Jos-Luijten/online-radiation-lab-robot/design and models of mechanics/Polymer sheet pmma models/tube binder left v1.step

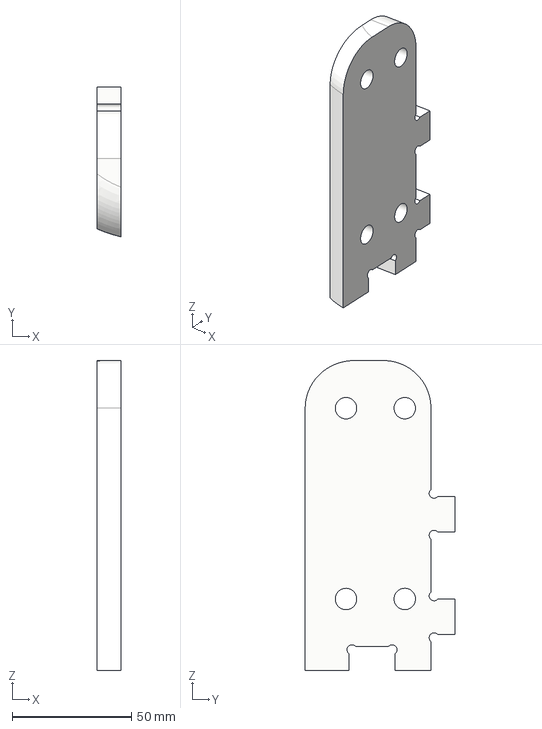
[picture p20: CAD file, 2024-03-11]
design and models of mechanics/Polymer sheet pmma models/tube binder left v1.step
10.0 x 62.8 x 130.0 mm
