Jos-Luijten/online-radiation-lab-robot/design and models of mechanics/objects from other vendors/corner bracket for 20x20 rail v1.step

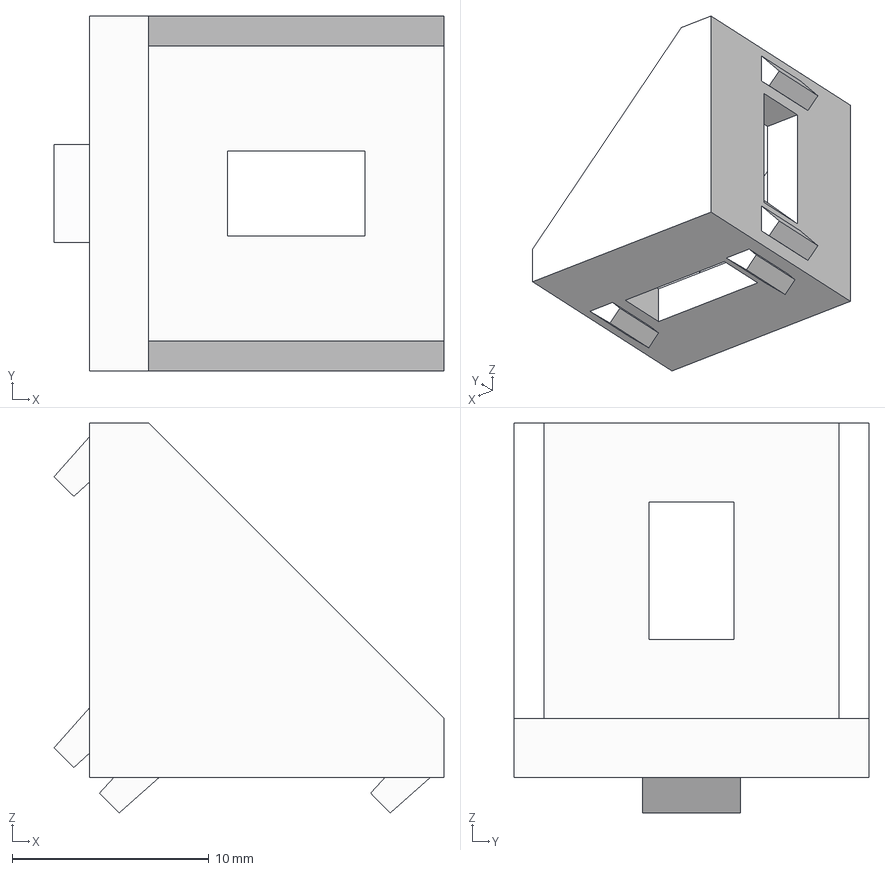
[picture p21: CAD file, 2024-03-11]
design and models of mechanics/objects from other vendors/corner bracket for 20x20 rail v1.step
19.8 x 18.0 x 19.8 mm
