Jos-Luijten/online-radiation-lab-robot/design and models of mechanics/Polymer sheet pmma models/base plate v1.step

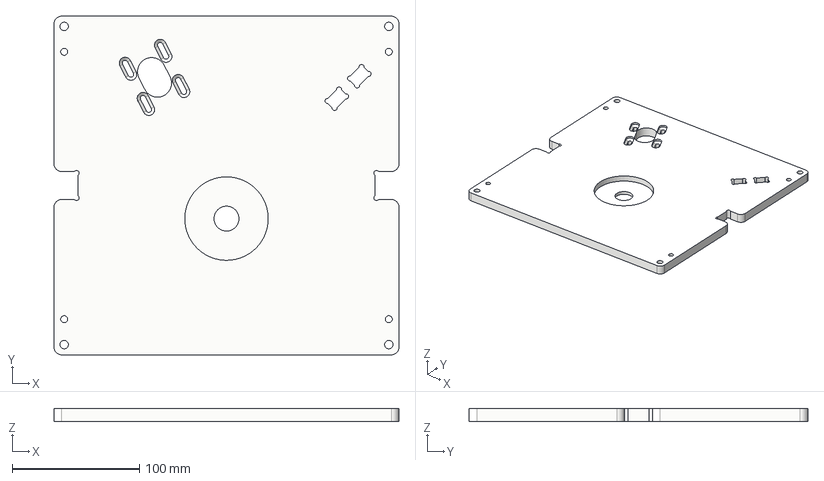
[picture p22: CAD file, 2024-03-11]
design and models of mechanics/Polymer sheet pmma models/base plate v1.step
271.0 x 266.0 x 10.0 mm
