Jos-Luijten/online-radiation-lab-robot/design and models of mechanics/objects from other vendors/T connector for 20x20 rail v1.step

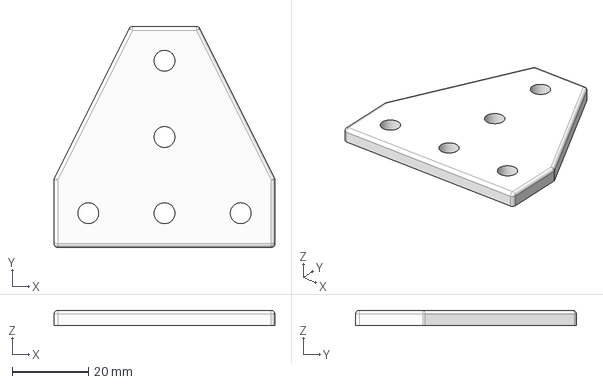
[picture p23: CAD file, 2024-03-11]
design and models of mechanics/objects from other vendors/T connector for 20x20 rail v1.step
58.0 x 58.0 x 4.00 mm
