Jos-Luijten/online-radiation-lab-robot/design and models of mechanics/Polymer sheet pmma models/rotation sensor plate v1.step

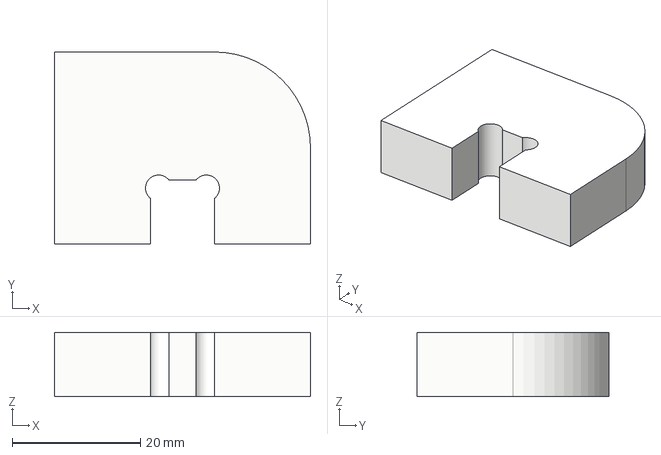
[picture p24: CAD file, 2024-03-11]
design and models of mechanics/Polymer sheet pmma models/rotation sensor plate v1.step
40.0 x 30.0 x 10.0 mm
