Jos-Luijten/online-radiation-lab-robot/design and models of mechanics/objects from other vendors/bracket for nema 17 v1.step

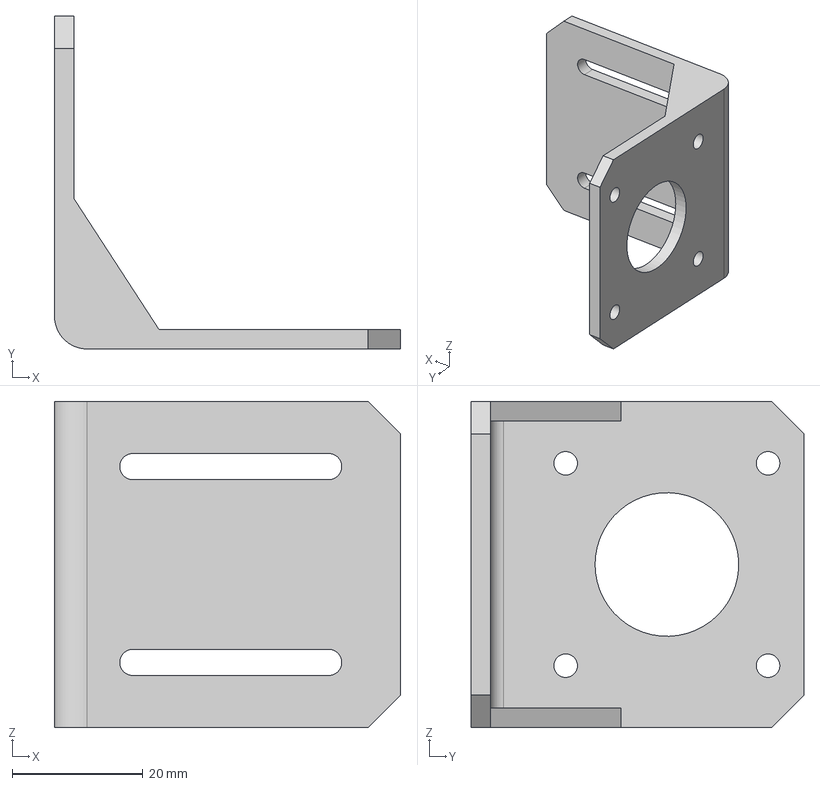
[picture p25: CAD file, 2024-03-11]
design and models of mechanics/objects from other vendors/bracket for nema 17 v1.step
53.0 x 51.0 x 50.0 mm
