Jos-Luijten/online-radiation-lab-robot/design and models of mechanics/objects from other vendors/thrust bearing - skf 51109 v1.step

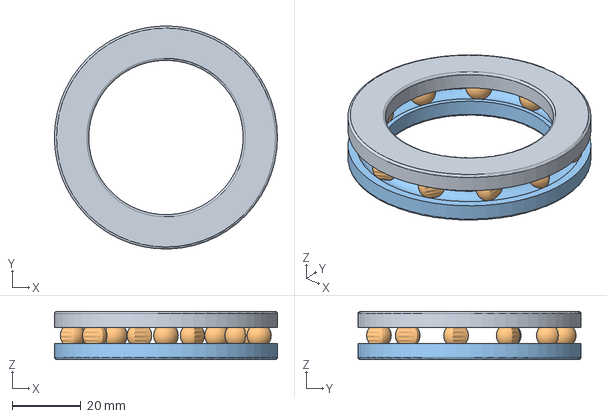
[picture p26: CAD file, 2024-03-11]
design and models of mechanics/objects from other vendors/thrust bearing - skf 51109 v1.step
65.0 x 65.0 x 14.0 mm
