Jos-Luijten/online-radiation-lab-robot/design and models of mechanics/objects from other vendors/aluminium extrusie 20x20x900mm v1.step

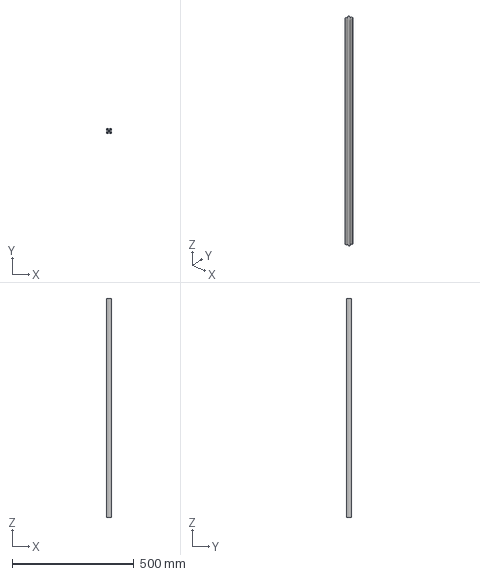
[picture p27: CAD file, 2024-03-11]
design and models of mechanics/objects from other vendors/aluminium extrusie 20x20x900mm v1.step
20.0 x 20.0 x 900.0 mm
