Jos-Luijten/online-radiation-lab-robot/design and models of mechanics/Polymer sheet pmma models/1x - elevator base plate.step

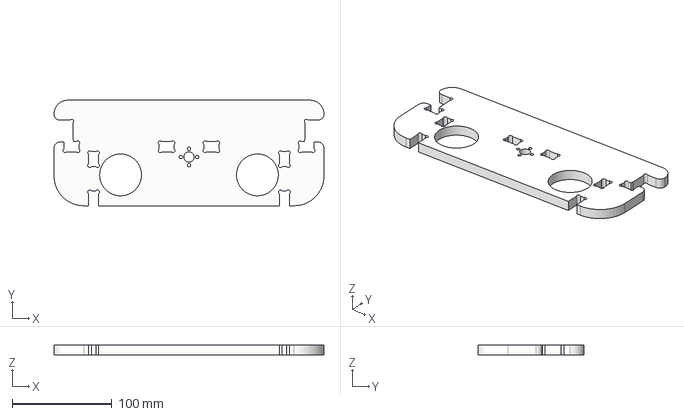
[picture p29: CAD file, 2024-03-11]
design and models of mechanics/Polymer sheet pmma models/1x - elevator base plate.step
271.0 x 106.0 x 10.0 mm
