Jos-Luijten/online-radiation-lab-robot/design and models of mechanics/objects from other vendors/Nema 17 groot v1.step

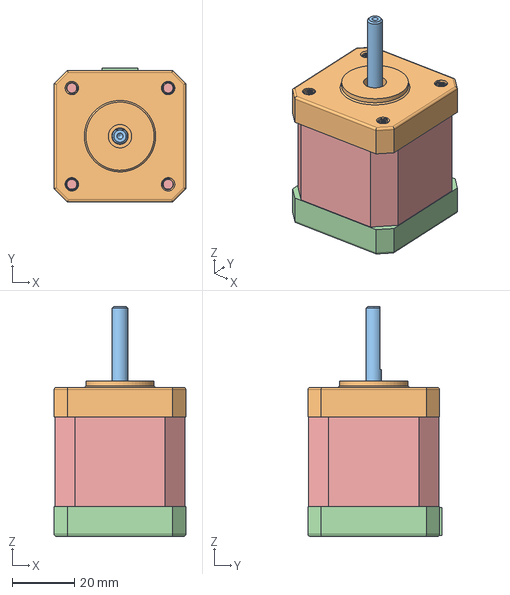
[picture p30: CAD file, 2024-03-11]
design and models of mechanics/objects from other vendors/Nema 17 groot v1.step
42.4 x 43.2 x 74.0 mm
