Jos-Luijten/online-radiation-lab-robot/design and models of mechanics/Polymer sheet pmma models/2x - tube binder left.step

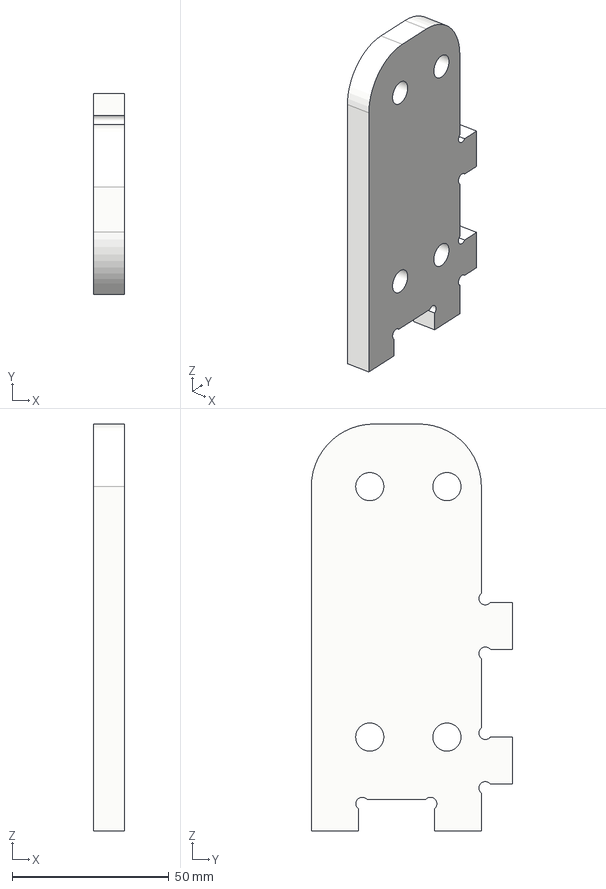
[picture p31: CAD file, 2024-03-11]
design and models of mechanics/Polymer sheet pmma models/2x - tube binder left.step
10.0 x 64.3 x 130.0 mm
