Jos-Luijten/online-radiation-lab-robot/design and models of mechanics/objects from other vendors/aluminium extrusie 20x20x270mm v1.step

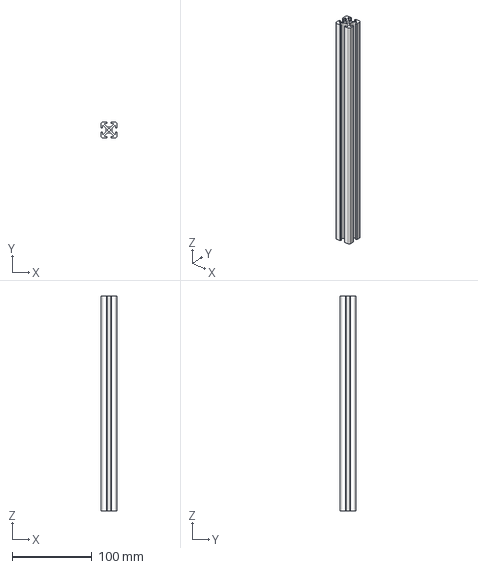
[picture p32: CAD file, 2024-03-11]
design and models of mechanics/objects from other vendors/aluminium extrusie 20x20x270mm v1.step
20.0 x 20.0 x 270.0 mm
