Jos-Luijten/online-radiation-lab-robot/design and models of mechanics/objects from other vendors/Flexible coupler 5mm to 8mm v1.step

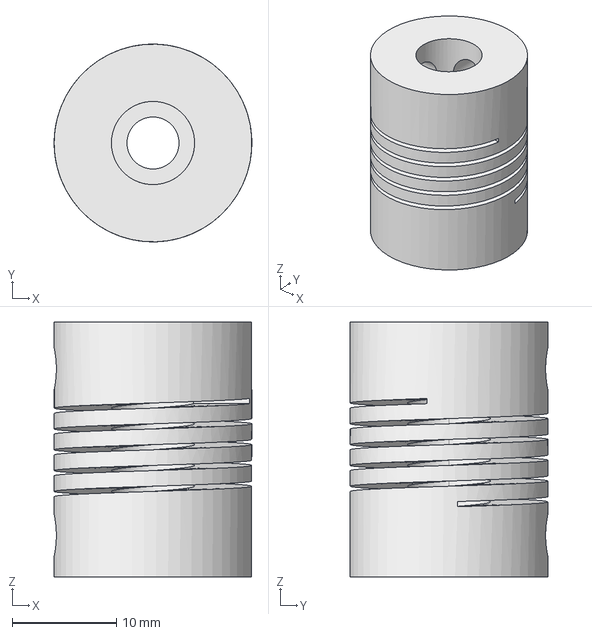
[picture p33: CAD file, 2024-03-11]
design and models of mechanics/objects from other vendors/Flexible coupler 5mm to 8mm v1.step
19.0 x 19.0 x 24.5 mm
