Jos-Luijten/online-radiation-lab-robot/design and models of mechanics/Polymer sheet pmma models/1x - tube buttress.step

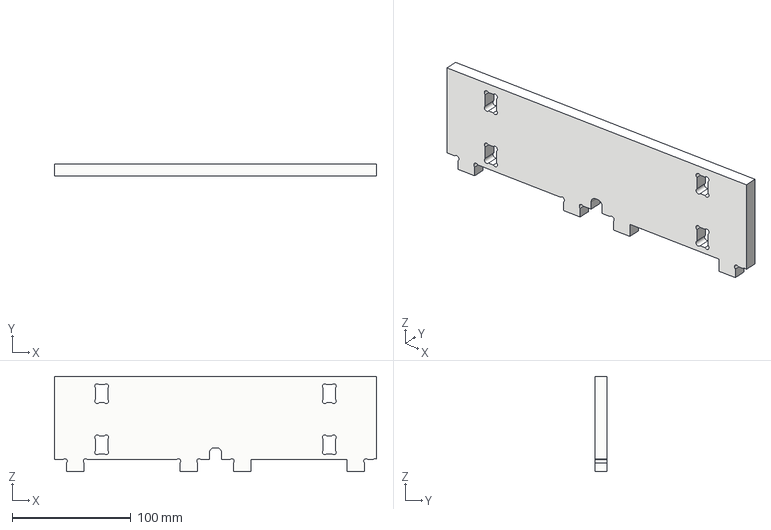
[picture p34: CAD file, 2024-03-11]
design and models of mechanics/Polymer sheet pmma models/1x - tube buttress.step
271.0 x 10.0 x 80.0 mm
