Jos-Luijten/online-radiation-lab-robot/design and models of mechanics/Polymer sheet pmma models/1x - intermediate pmma.step

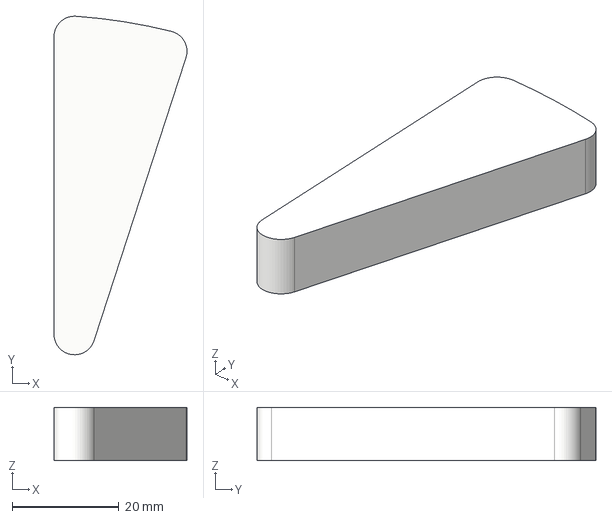
[picture p35: CAD file, 2024-03-11]
design and models of mechanics/Polymer sheet pmma models/1x - intermediate pmma.step
24.9 x 63.5 x 10.0 mm
